WildfootW/NTU-BIME_Final-Project/Software/Components/HC-SR04/HC-SR04-RPi.GPIO.py

#Libraries
import RPi.GPIO as GPIO
import time
import signal
 
#GPIO Mode (BOARD / BCM)
GPIO.setmode(GPIO.BOARD)
 
#set GPIO Pins
GPIO_TRIGGER = 12
GPIO_ECHO = 18
GPIO_TRIGGER = 40
GPIO_ECHO = 38
 
#set GPIO direction (IN / OUT)
GPIO.setup(GPIO_TRIGGER, GPIO.OUT)
GPIO.setup(GPIO_ECHO, GPIO.IN)
 
def distance():
    GPIO.output(GPIO_TRIGGER, False)
    time.sleep(0.000002)
    GPIO.output(GPIO_TRIGGER, True)
    time.sleep(0.00001)
    GPIO.output(GPIO_TRIGGER, False)
 
    StartTime = time.time()
    StopTime = time.time()
 
    # save StartTime
    while GPIO.input(GPIO_ECHO) == 0:
        StartTime = time.time()
 
    # save time of arrival
    while GPIO.input(GPIO_ECHO) == 1:
        StopTime = time.time()
 
    # time difference between start and arrival
    TimeElapsed = StopTime - StartTime
    # multiply with the sonic speed (34300 cm/s)
    # and divide by 2, because there and back
    distance = (TimeElapsed * 34300) / 2
 
    return distance

def handler(signum, frame):
    raise TimeoutError()
 
if __name__ == '__main__':
    try:
        while True:
            try:
                signal.signal(signal.SIGALRM, handler)
                signal.alarm(2)
                dist = distance()
                signal.alarm(0)
                print ("Measured Distance = %.1f cm" % dist)
            except TimeoutError:
                print("Forever is over!")
            time.sleep(1)
 
        # Reset by pressing CTRL + C
    except KeyboardInterrupt:
        print("Measurement stopped by User")
        GPIO.cleanup()
